kernalix7/DiveChecker/website/assets/images/og-divechecker.jpg

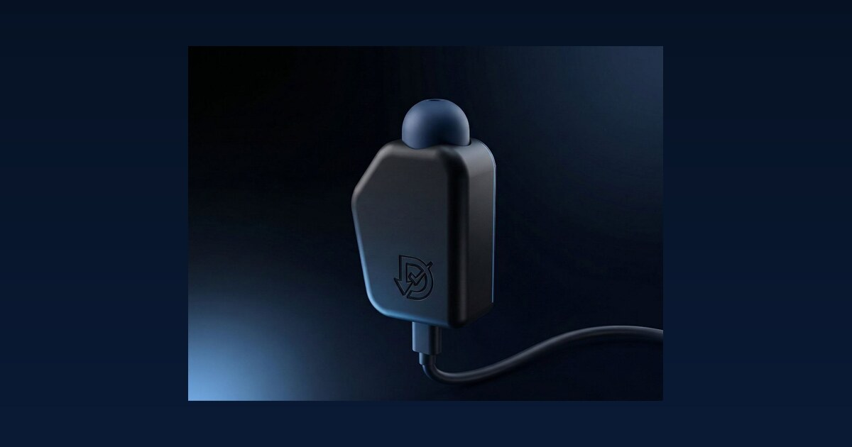
website/assets/images/og-divechecker.jpg
