kernalix7/DiveChecker/website/assets/images/feature-usage.jpg

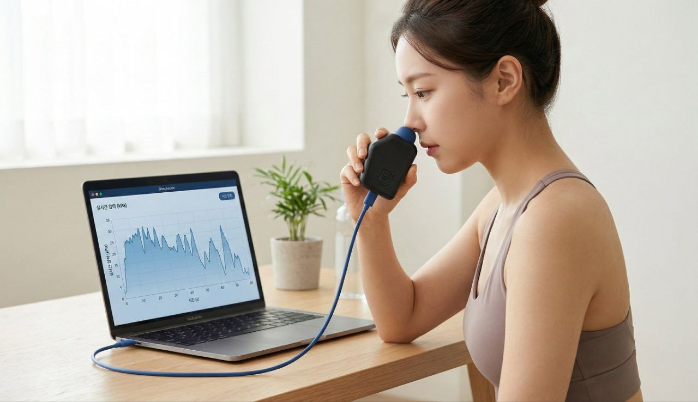
website/assets/images/feature-usage.jpg
